TheGrayGryphon/ARA-Replicator-Run8/miniRDkicad/miniRDkicad.kicad_sch

## KiCad design miniRDkicad/miniRDkicad.kicad_sch (2024-05-03)

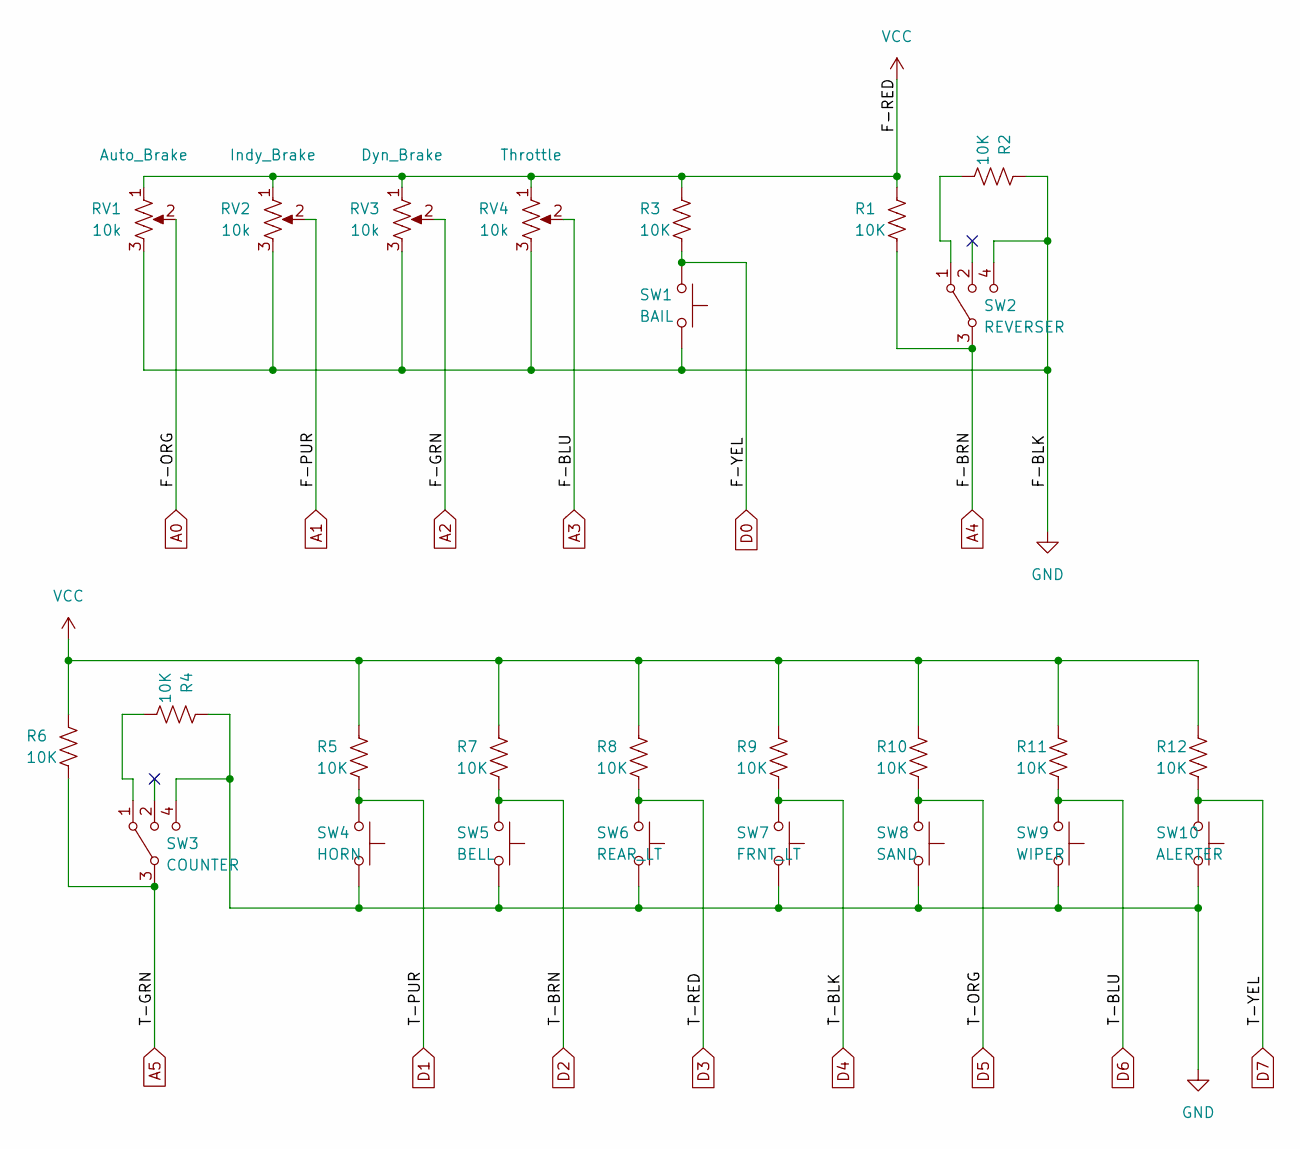
[picture p3: schematic miniRDkicad.kicad_sch]

Parts:
R1, R2, R3, R4, R5, R6, R7, R8, R9, R10, R11, R12: 10K
RV1, RV2, RV3, RV4: 10k
SW1: BAIL
SW2: REVERSER
SW3: COUNTER
SW4: HORN
SW5: BELL
SW6: REAR_LT
SW7: FRNT_LT
SW8: SAND
SW9: WIPER
SW10: ALERTER

Connections:
A0: RV1.2
A1: RV2.2
A2: RV3.2
A3: RV4.2
A4: R1.2, SW2.3
A5: R6.2, SW3.3
D0: R3.2, SW1.1
D1: R5.2, SW4.1
D2: R7.2, SW5.1
D3: R8.2, SW6.1
D4: R9.2, SW7.1
D5: R10.2, SW8.1
D6: R11.2, SW9.1
D7: R12.2, SW10.1
GND: R2.1, R4.1, RV1.3, RV2.3, RV3.3, RV4.3, SW1.2, SW2.4, SW3.4, SW4.2, SW5.2, SW6.2, SW7.2, SW8.2, SW9.2, SW10.2
unnamed: R2.2, SW2.1
unnamed: R4.2, SW3.1
VCC: R1.1, R3.1, R5.1, R6.1, R7.1, R8.1, R9.1, R10.1, R11.1, R12.1, RV1.1, RV2.1, RV3.1, RV4.1
